atrvicky/Console/renders/front.jpg

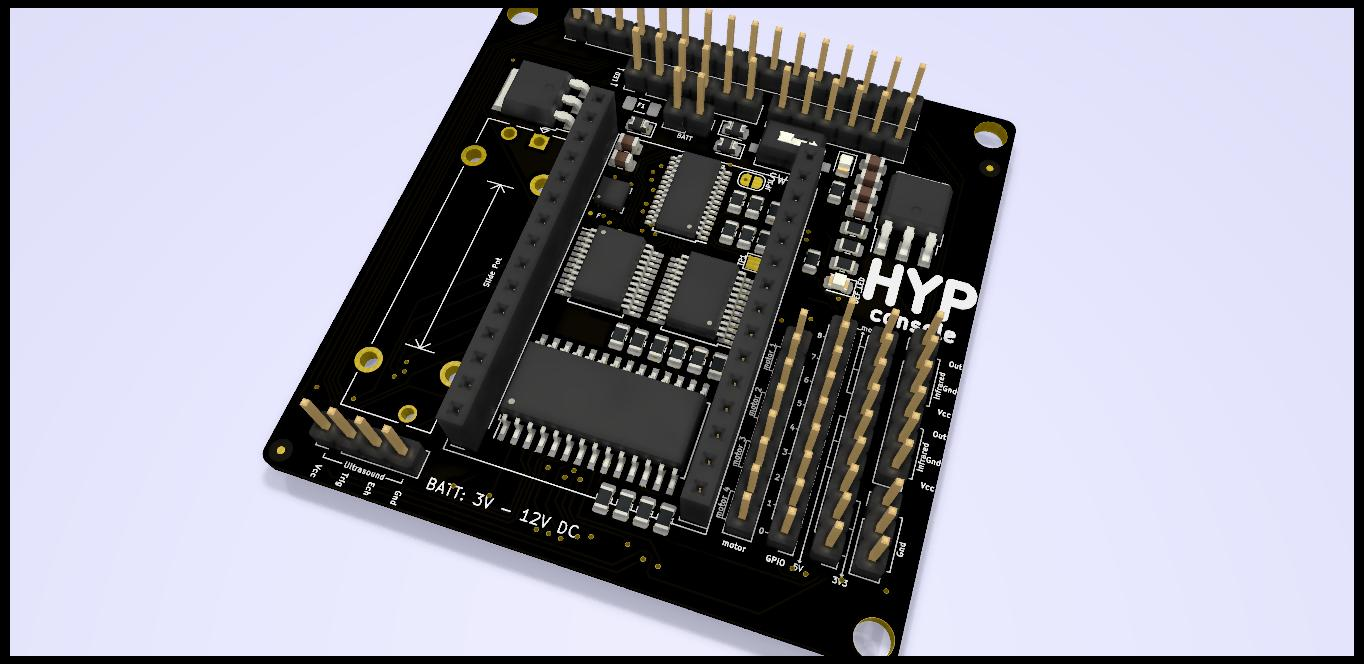
renders/front.jpg
