atrvicky/Console/renders/ir.jpg

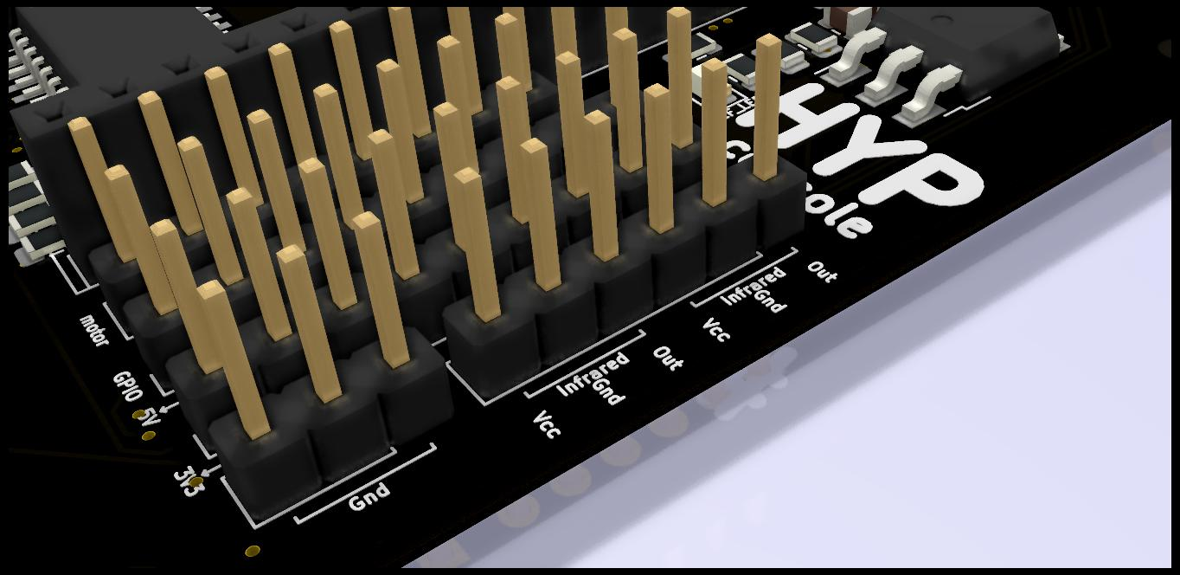
renders/ir.jpg
