atrvicky/Console/plots/pdf/F_SilkS.pdf

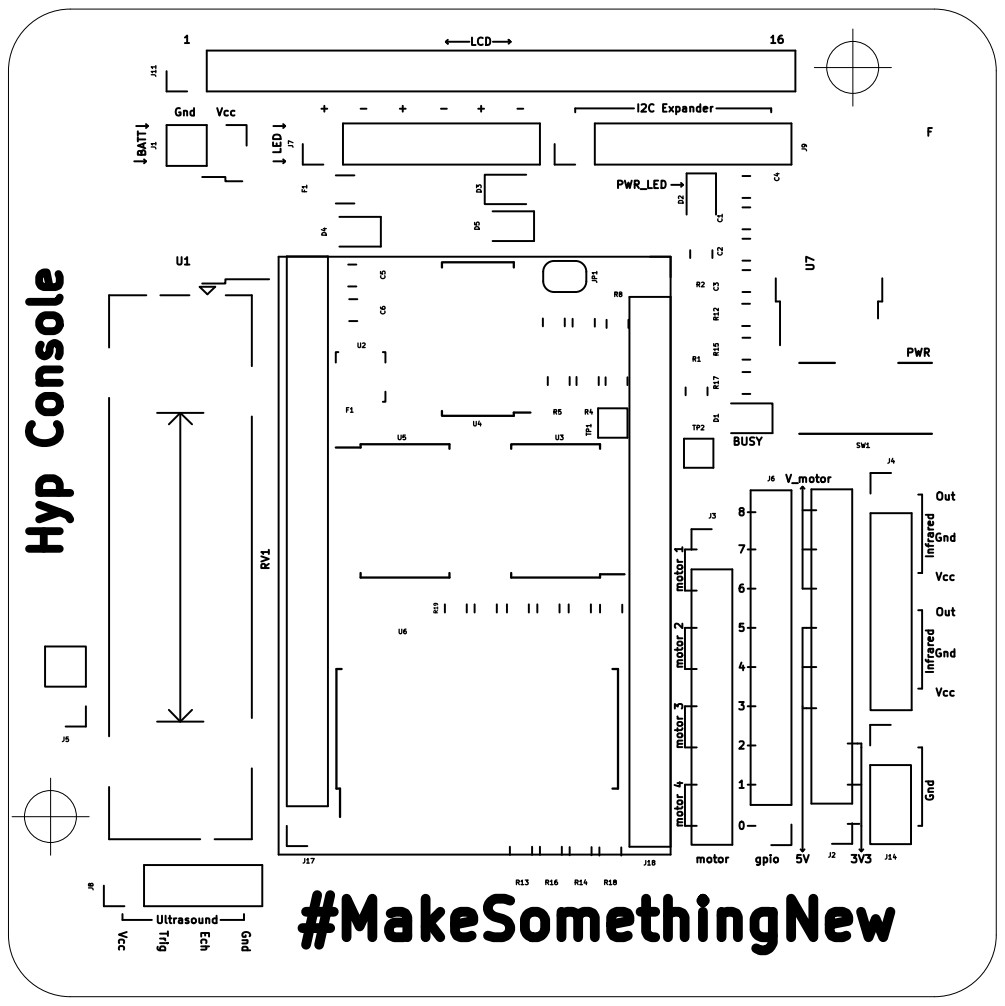
[picture p18: page 1]
